jochenneumaier/TLC-spotting-device/CAD files/02_Z_Gear_Wheel.stp

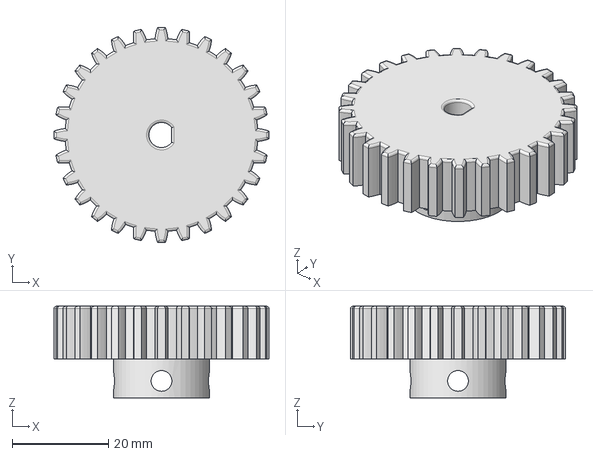
[picture p23: CAD file, 2024-06-07]
CAD files/02_Z_Gear_Wheel.stp
44.6 x 44.6 x 19.0 mm
