jochenneumaier/TLC-spotting-device/CAD files/21_Table.stp

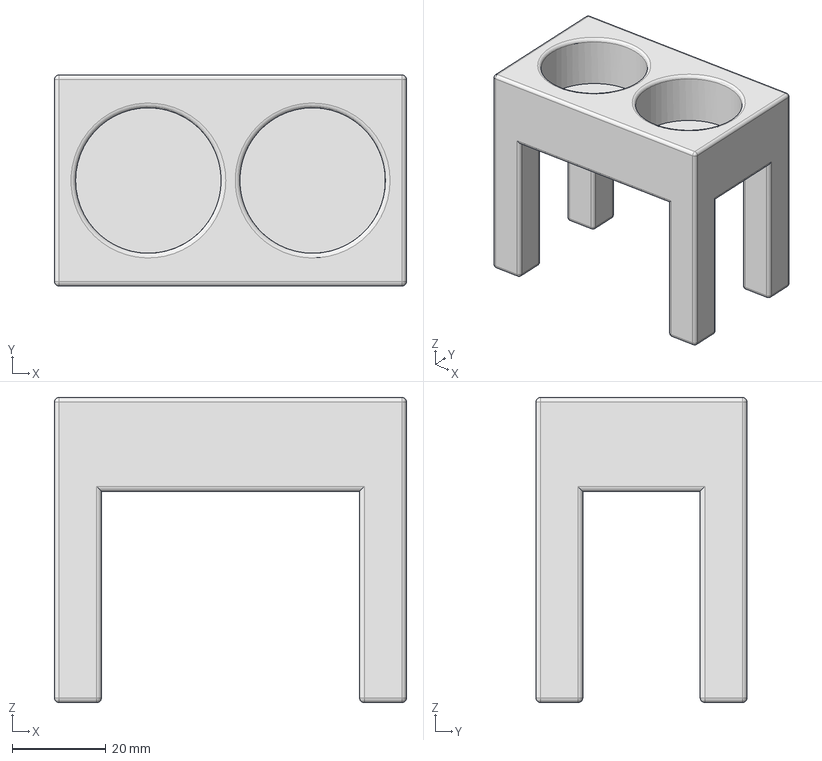
[picture p24: CAD file, 2024-06-07]
CAD files/21_Table.stp
75.0 x 45.0 x 65.0 mm
