jochenneumaier/TLC-spotting-device/CAD files/06_SP_Bottom.stp

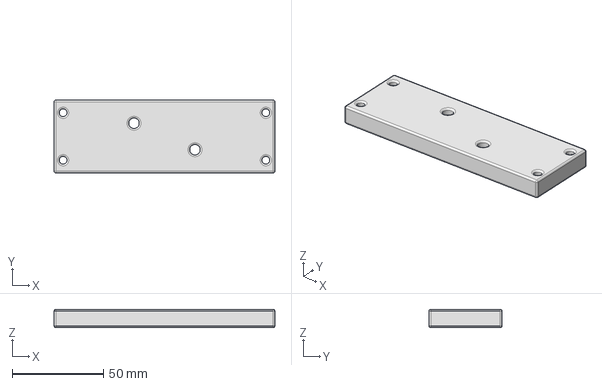
[picture p25: CAD file, 2024-06-07]
CAD files/06_SP_Bottom.stp
121.0 x 40.0 x 10.0 mm
