jochenneumaier/TLC-spotting-device/CAD files/17_PS_Rack_X.stp

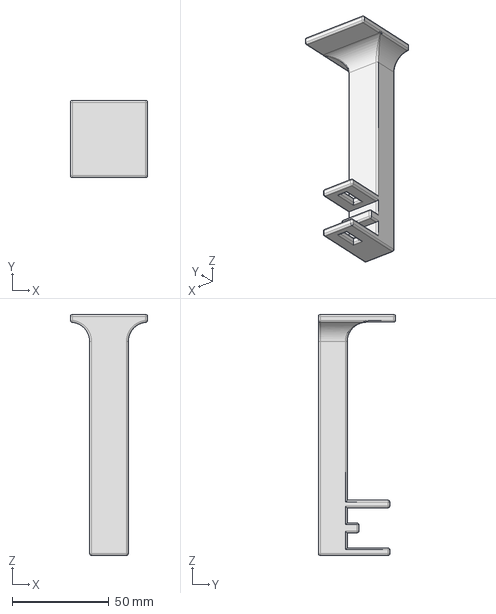
[picture p26: CAD file, 2024-06-07]
CAD files/17_PS_Rack_X.stp
40.0 x 40.0 x 124.6 mm
