jochenneumaier/TLC-spotting-device/CAD files/04_SP_Top.stp

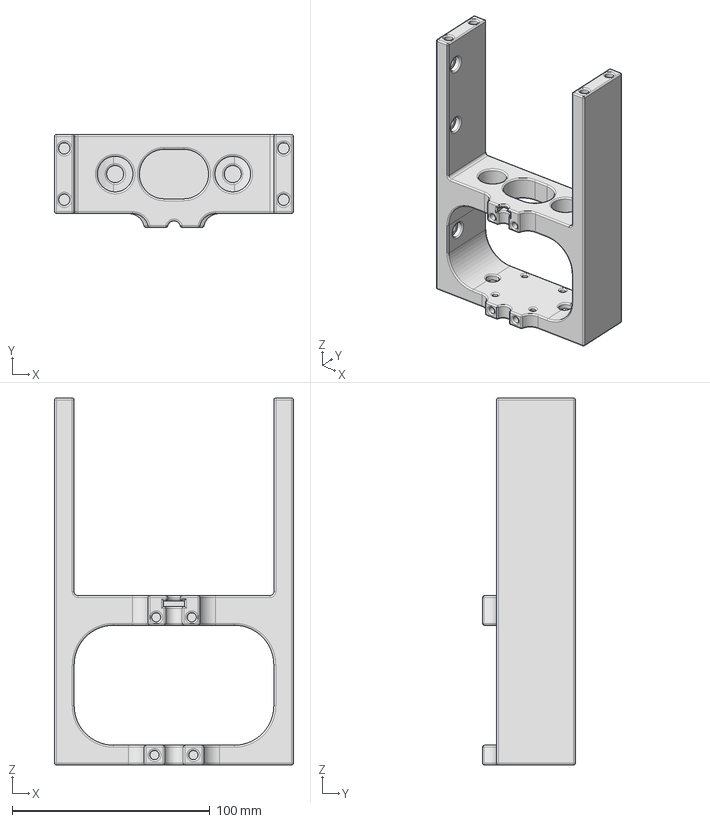
[picture p27: CAD file, 2024-06-07]
CAD files/04_SP_Top.stp
121.0 x 47.0 x 185.7 mm
