jochenneumaier/TLC-spotting-device/CAD files/03.2_Z_Gear_Fixation.stp

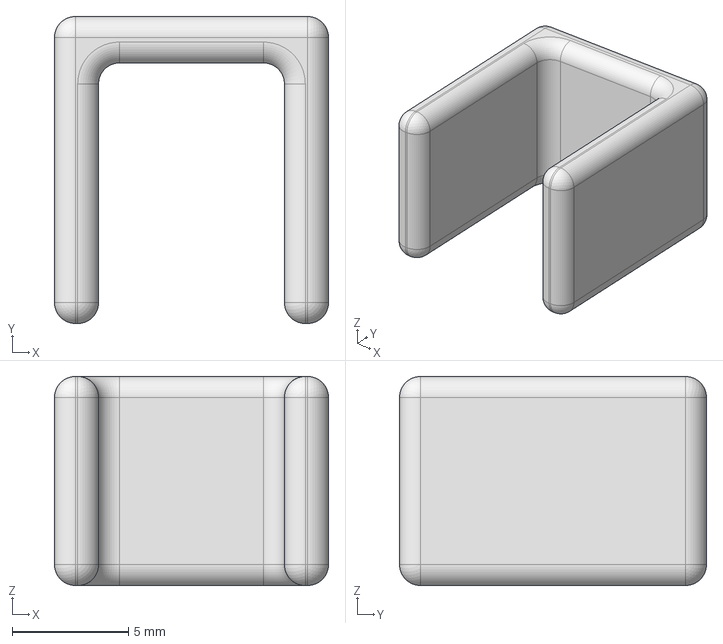
[picture p28: CAD file, 2024-06-07]
CAD files/03.2_Z_Gear_Fixation.stp
11.8 x 13.2 x 9.00 mm
