jochenneumaier/TLC-spotting-device/CAD files/07_SP_Clamp1.stp

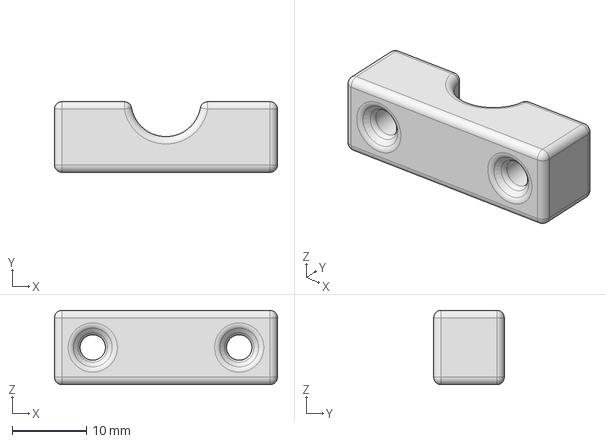
[picture p29: CAD file, 2024-06-07]
CAD files/07_SP_Clamp1.stp
30.0 x 9.50 x 10.0 mm
