jochenneumaier/TLC-spotting-device/CAD files/11_BT_left.stp

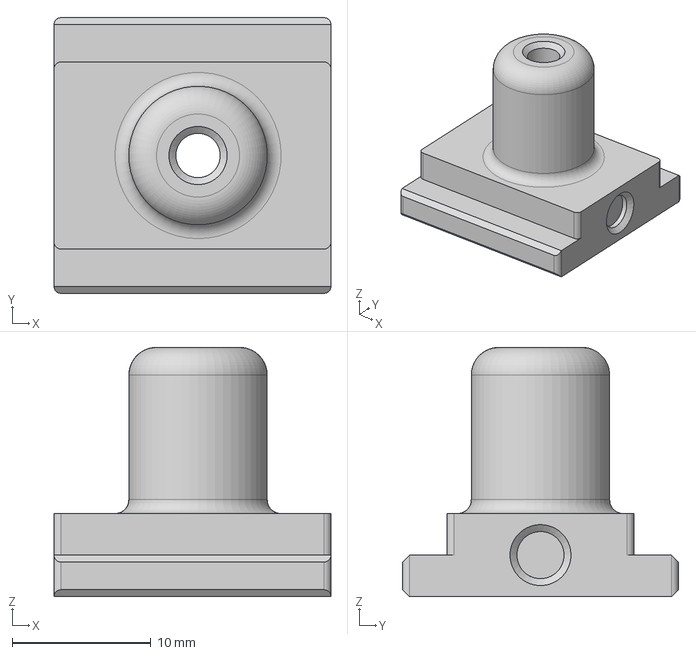
[picture p30: CAD file, 2024-06-07]
CAD files/11_BT_left.stp
20.0 x 19.9 x 18.0 mm
